Spirik/HDDc/mark-03/export/HDD-Clicker-Mark-03_bb_edited_export_bg.png

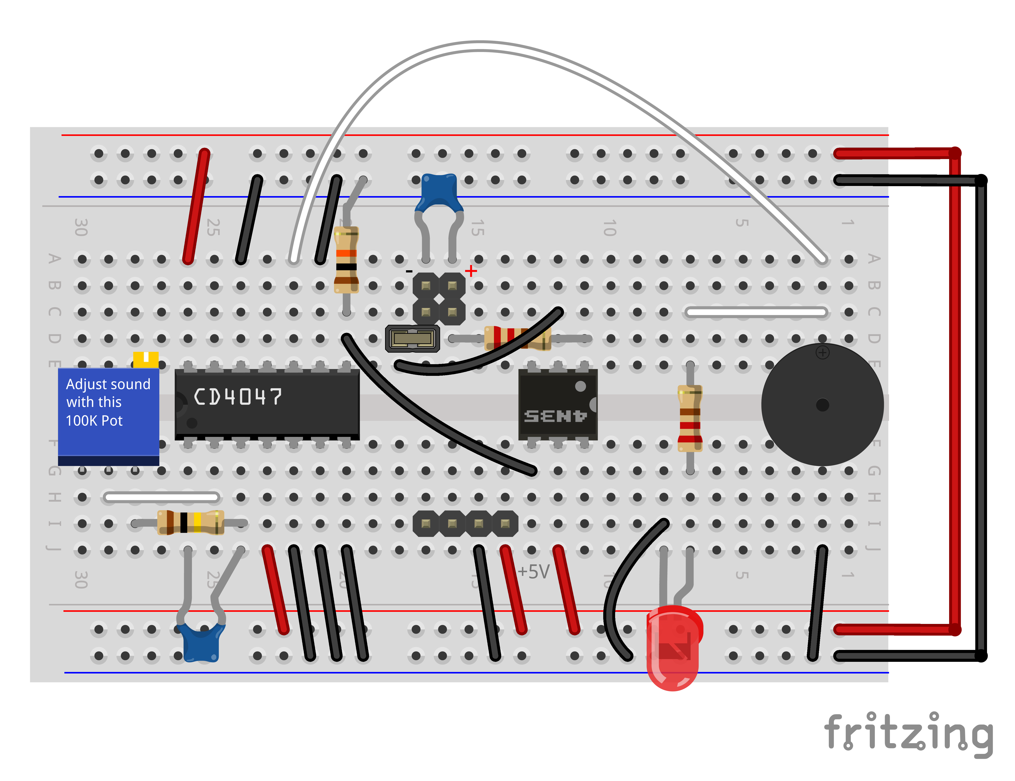
mark-03/export/HDD-Clicker-Mark-03_bb_edited_export_bg.png
