Spirik/HDDc/mark-03/export/IMG_8242-1_edited_o.jpg

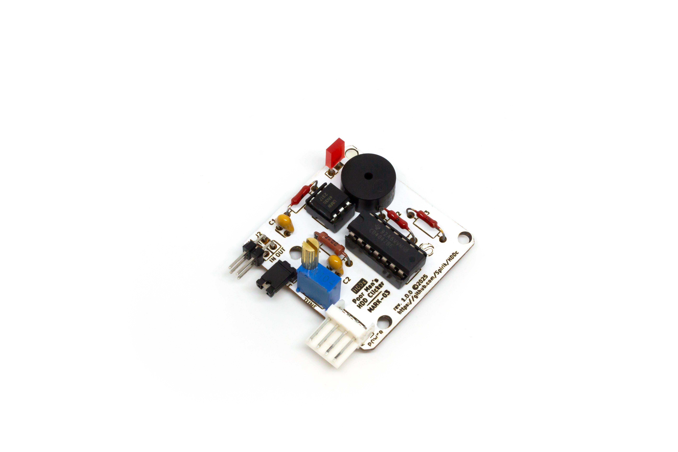
mark-03/export/IMG_8242-1_edited_o.jpg
