Spirik/HDDc/mark-03/export/IMG_8247-1_edited_o.jpg

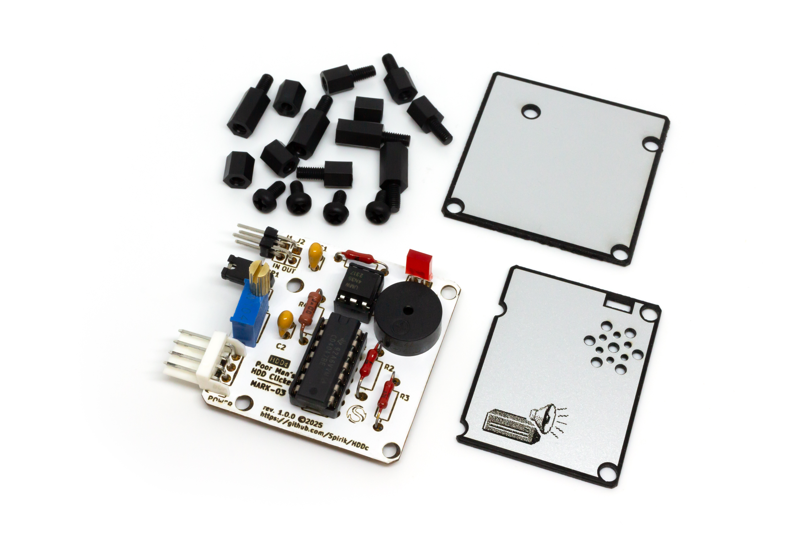
mark-03/export/IMG_8247-1_edited_o.jpg
