Spirik/HDDc/mark-03/pcb/diy/hddc_mark-03_v1_top-silk_black_edited_export.png

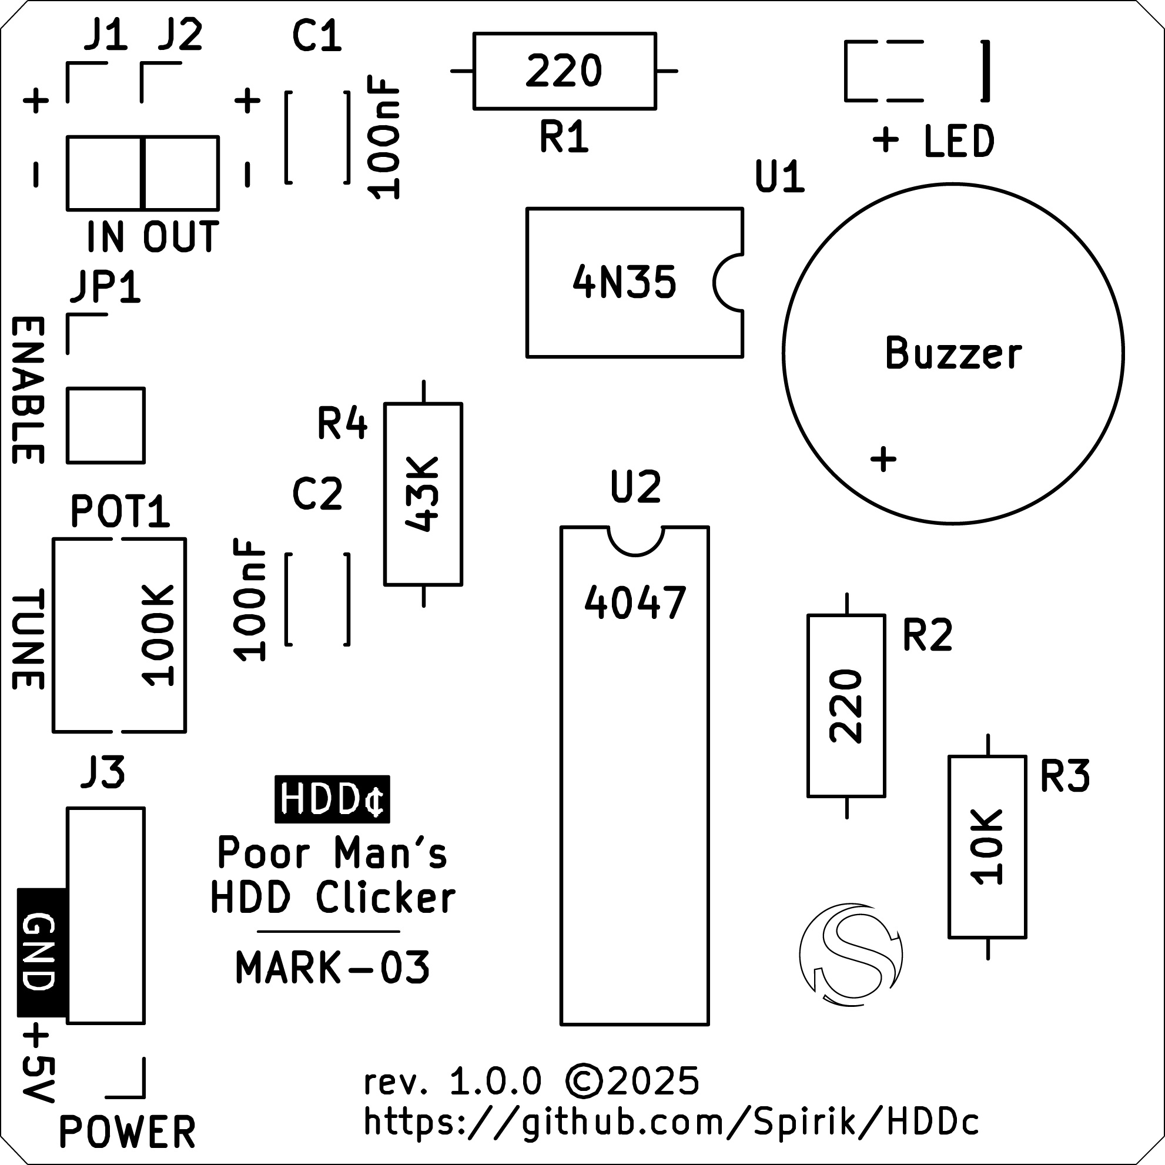
mark-03/pcb/diy/hddc_mark-03_v1_top-silk_black_edited_export.png
