Spirik/HDDc/mark-03/pcb/enclosure/hddc-case_bottom_v1_border_export_41.9x41.9.png

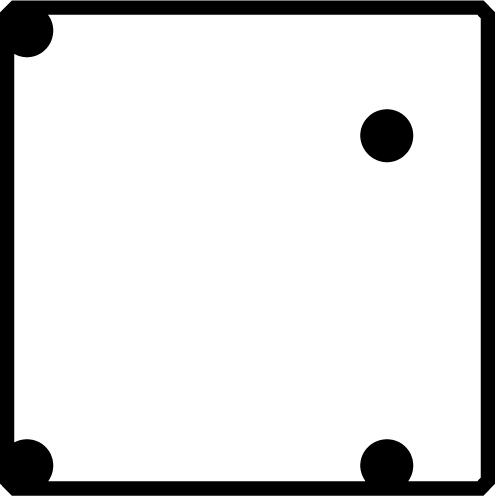
mark-03/pcb/enclosure/hddc-case_bottom_v1_border_export_41.9x41.9.png
