Spirik/HDDc/mark-03/pcb/enclosure/hddc-case_top_v1_border_export_32.745x41.91.png

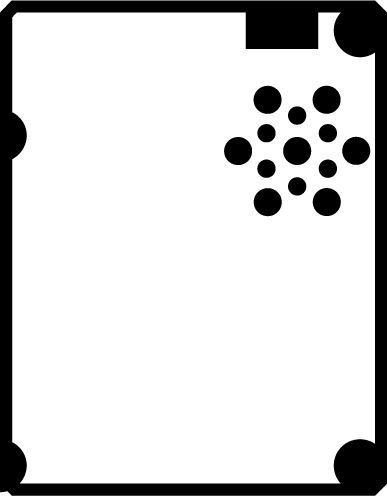
mark-03/pcb/enclosure/hddc-case_top_v1_border_export_32.745x41.91.png
