Spirik/HDDc/mark-03/pcb/render/HDD-Clicker-Mark-03_pcb-render_bare_top_edited.png

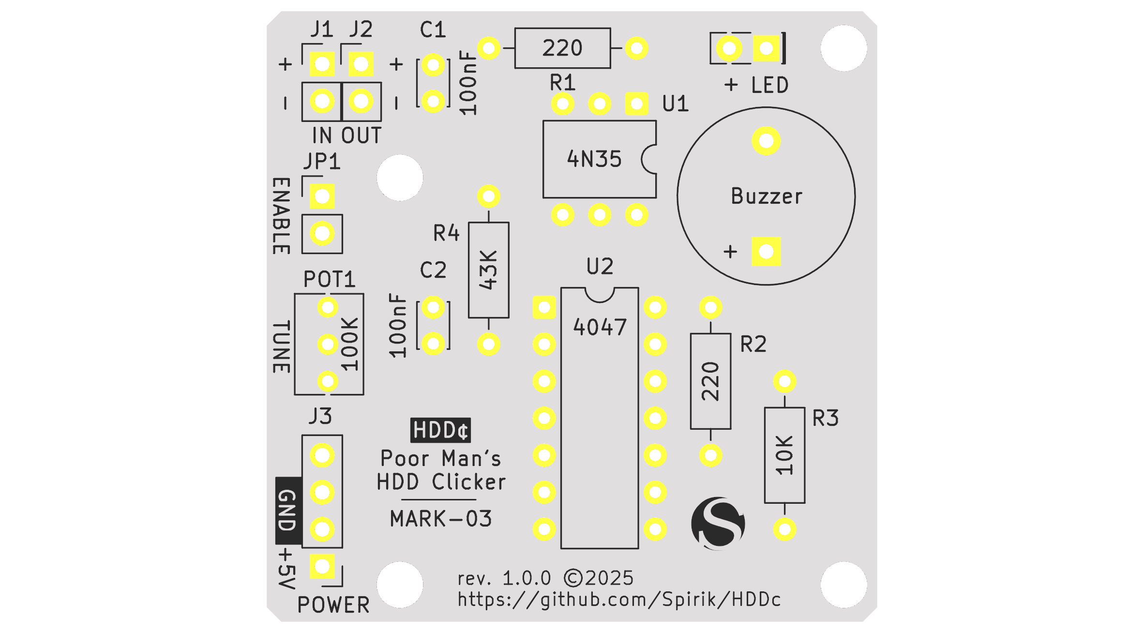
mark-03/pcb/render/HDD-Clicker-Mark-03_pcb-render_bare_top_edited.png
