Spirik/HDDc/mark-00/export/hddc_mark-00_v1_schematic_sheet.pdf

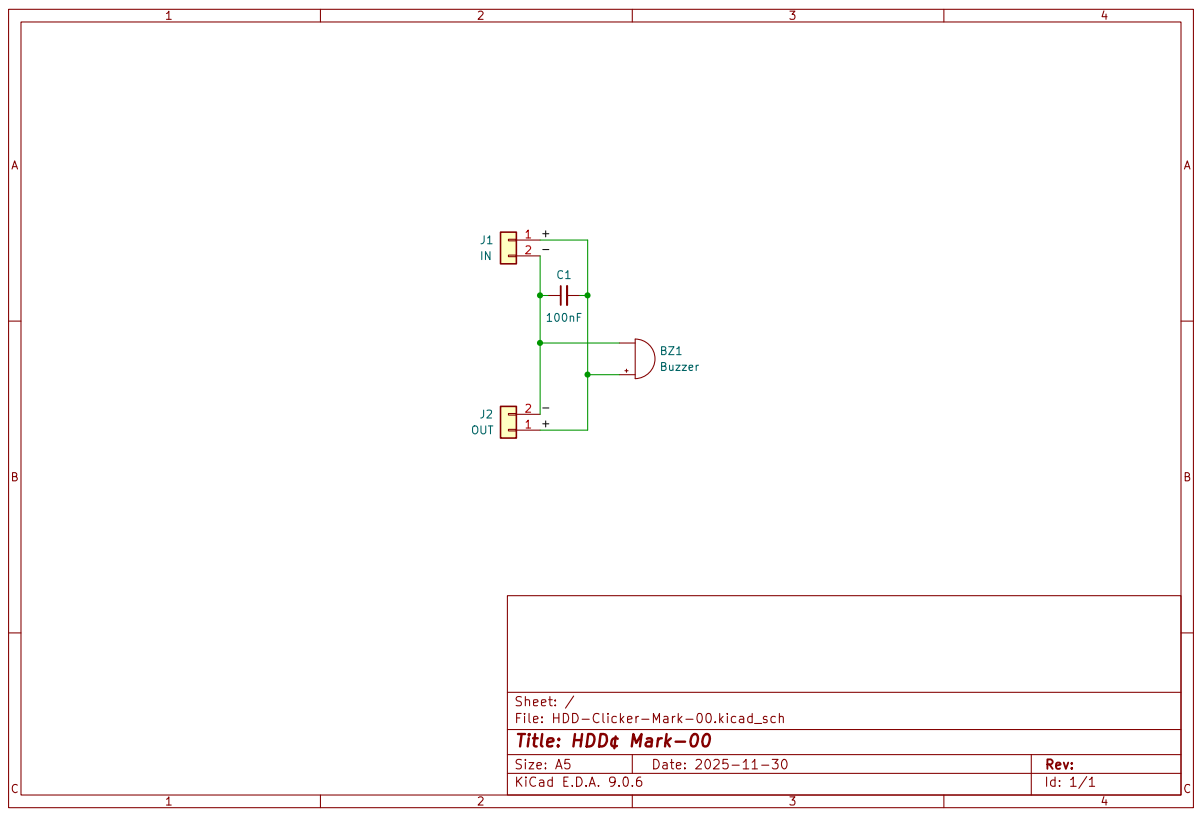
[picture p39: page 1]
